MOSH-Insa-Toulouse/2024-2025-4GP-GregoryBibiloni-GuillaumeBarth/Android/face arrière.png

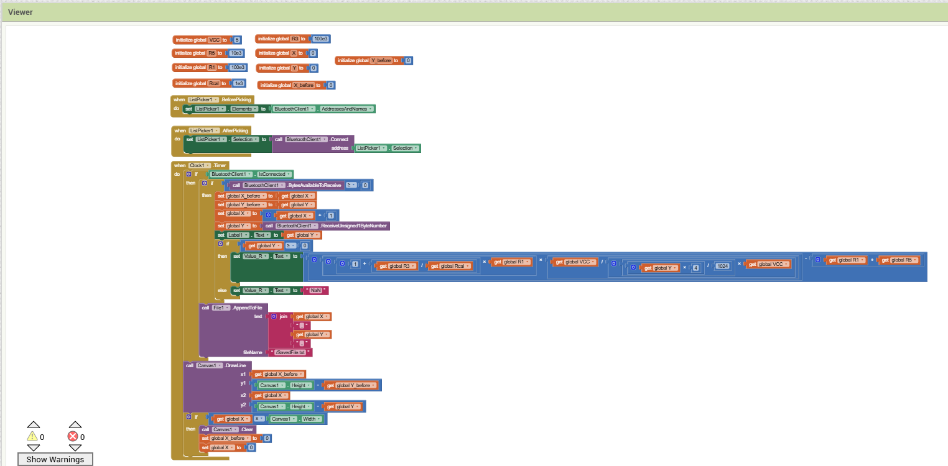
Android/face arrière.png
