MOSH-Insa-Toulouse/2024-2025-4GP-GregoryBibiloni-GuillaumeBarth/Android/face avant.png

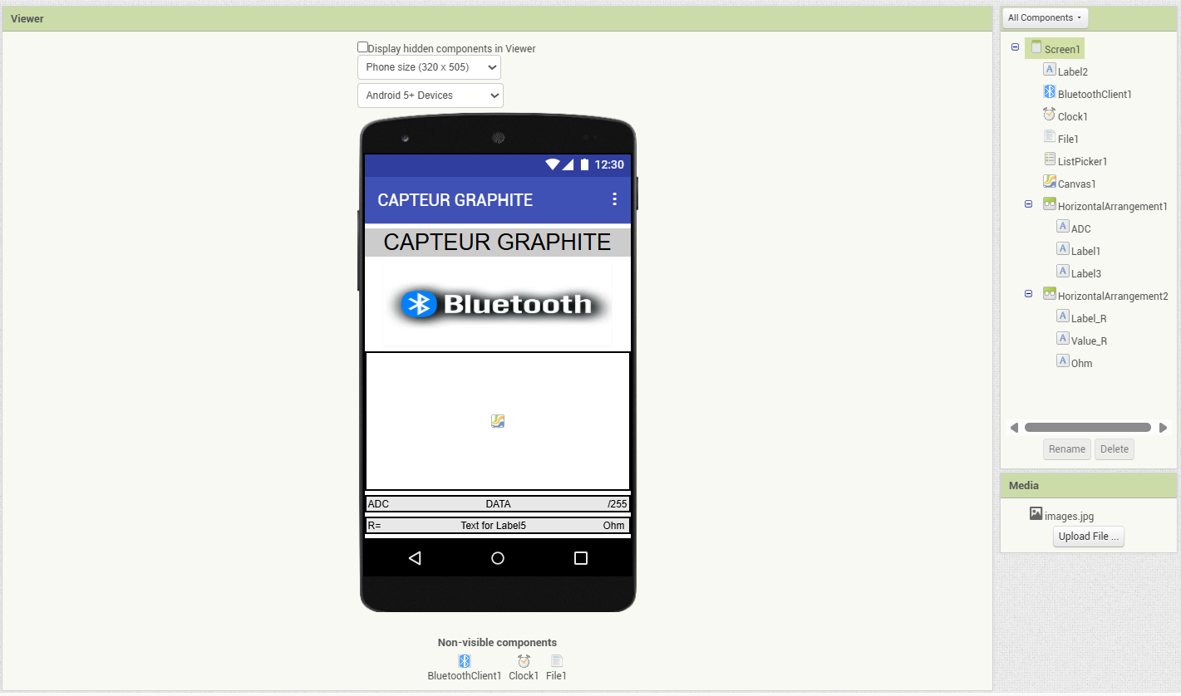
Android/face avant.png
