MOSH-Insa-Toulouse/2024-2025-4GP-GregoryBibiloni-GuillaumeBarth/KiCad/3D Models/4par1 female header/PBS1.27.png

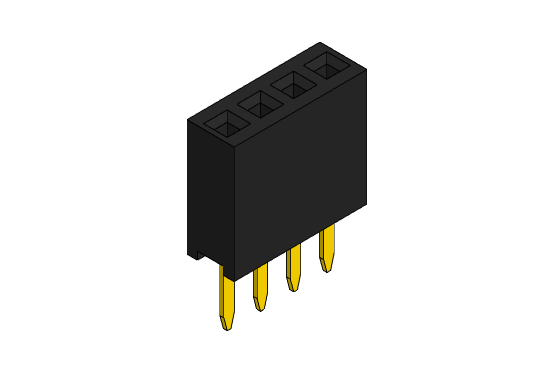
KiCad/3D Models/4par1 female header/PBS1.27.png
