MOSH-Insa-Toulouse/2024-2025-4GP-GregoryBibiloni-GuillaumeBarth/KiCad/3D Models/STEP/1x5.STEP

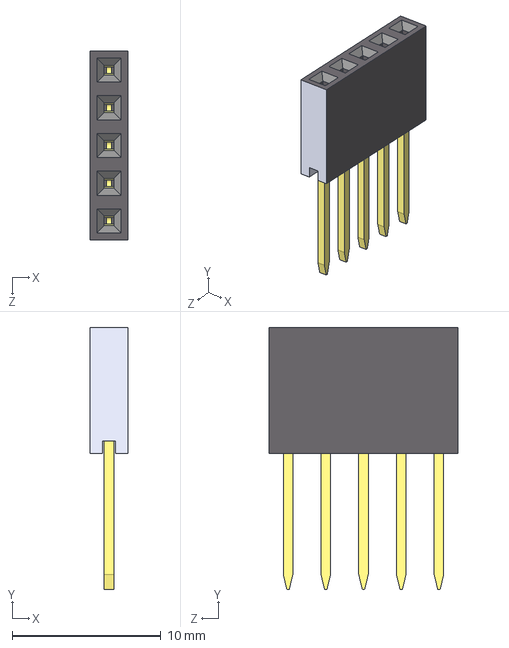
[picture p36: CAD file, 2025-03-13]
KiCad/3D Models/STEP/1x5.STEP
2.54 x 17.6 x 12.7 mm
