MOSH-Insa-Toulouse/2024-2025-4GP-GregoryBibiloni-GuillaumeBarth/KiCad/3D Models/Flex sensor/SolidEdge/FS-L-0095-103-ST - Top.stp

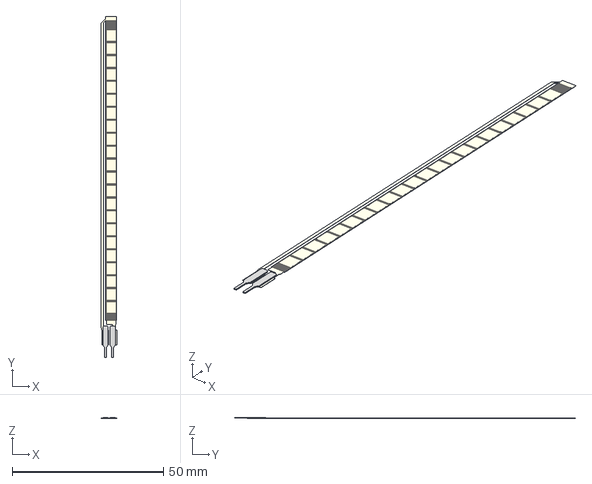
[picture p38: CAD file, 2025-03-13]
KiCad/3D Models/Flex sensor/SolidEdge/FS-L-0095-103-ST - Top.stp
5.17 x 112.8 x 0.292 mm
