MOSH-Insa-Toulouse/2024-2025-4GP-GregoryBibiloni-GuillaumeBarth/KiCad/3D Models/Rotary encodeur/Rotary Encoder -  ODG/sw2017 model/2.54 5PIN 90.SLDPRT

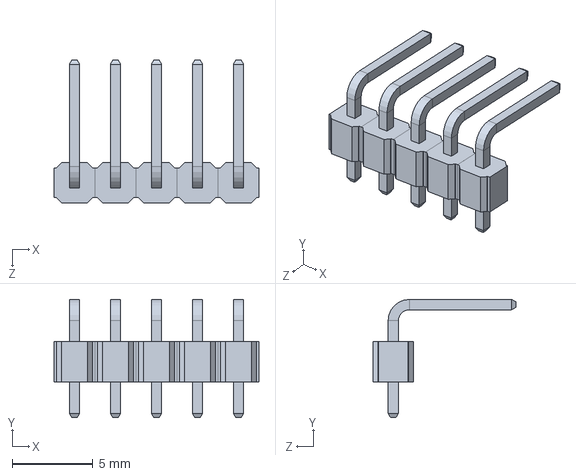
[picture p39: CAD file, 2025-03-13]
KiCad/3D Models/Rotary encodeur/Rotary Encoder - ODG/sw2017 model/2.54 5PIN 90.SLDPRT
12.7 x 7.32 x 8.85 mm
