MOSH-Insa-Toulouse/2024-2025-4GP-GregoryBibiloni-GuillaumeBarth/KiCad/3D Models/Rotary encodeur/Rotary Encoder -  ODG/sw2017 model/D-handle.SLDPRT

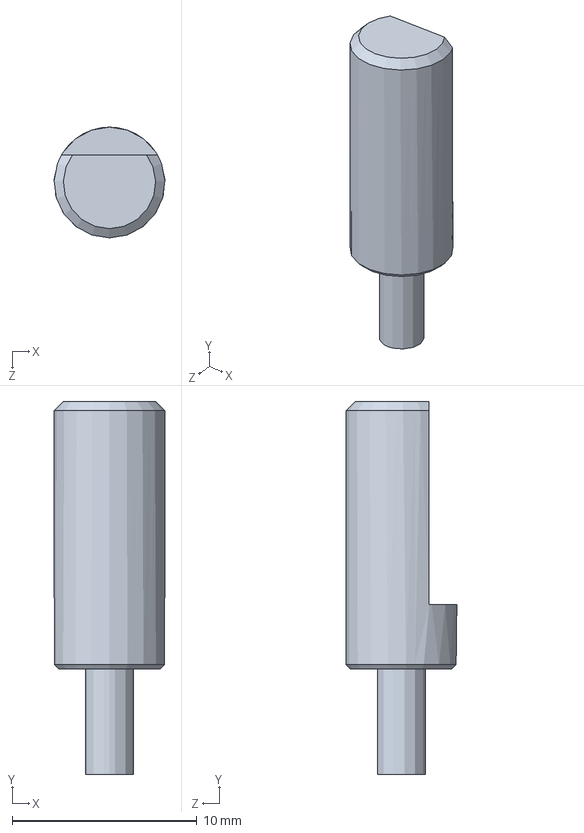
[picture p42: CAD file, 2025-03-13]
KiCad/3D Models/Rotary encodeur/Rotary Encoder - ODG/sw2017 model/D-handle.SLDPRT
6.00 x 20.2 x 6.00 mm
