MOSH-Insa-Toulouse/2024-2025-4GP-GregoryBibiloni-GuillaumeBarth/KiCad/3D Models/Rotary encodeur/Rotary Encoder -  ODG/sw2017 model/Rotary Encoder.SLDPRT

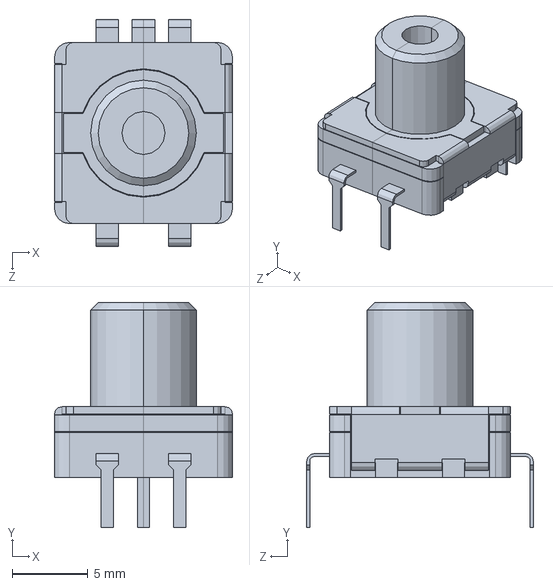
[picture p45: CAD file, 2025-03-13]
KiCad/3D Models/Rotary encodeur/Rotary Encoder - ODG/sw2017 model/Rotary Encoder.SLDPRT
11.8 x 14.9 x 15.0 mm
