MOSH-Insa-Toulouse/2024-2025-4GP-GregoryBibiloni-GuillaumeBarth/KiCad/3D Models/STEP/1x4.STEP

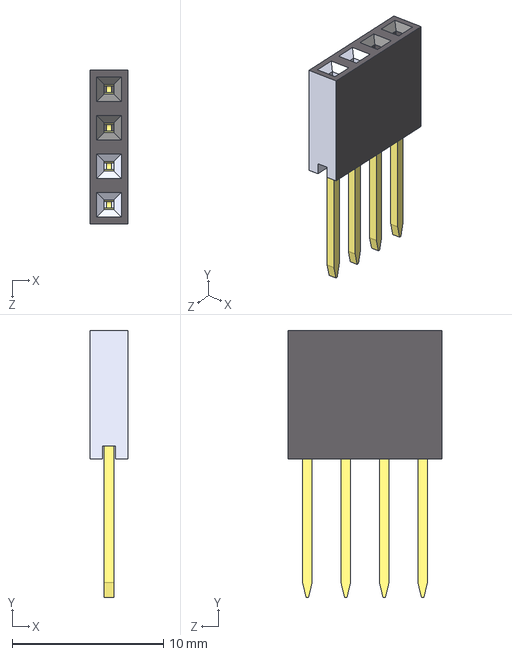
[picture p46: CAD file, 2025-03-13]
KiCad/3D Models/STEP/1x4.STEP
2.54 x 17.6 x 10.2 mm
