MOSH-Insa-Toulouse/2024-2025-4GP-GregoryBibiloni-GuillaumeBarth/KiCad/3D Models/4par1 female header/models3d/PBS1.27/PBS1.27-22R.step

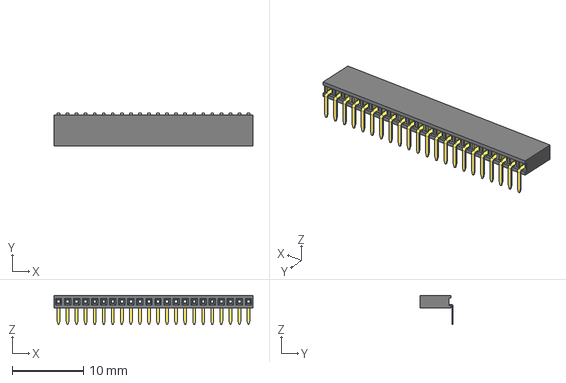
[picture p47: CAD file, 2025-03-13]
KiCad/3D Models/4par1 female header/models3d/PBS1.27/PBS1.27-22R.step
27.9 x 4.70 x 4.10 mm
