MOSH-Insa-Toulouse/2024-2025-4GP-GregoryBibiloni-GuillaumeBarth/KiCad/3D Models/STEP/pin header female 2.54mm_0.1in.STEP

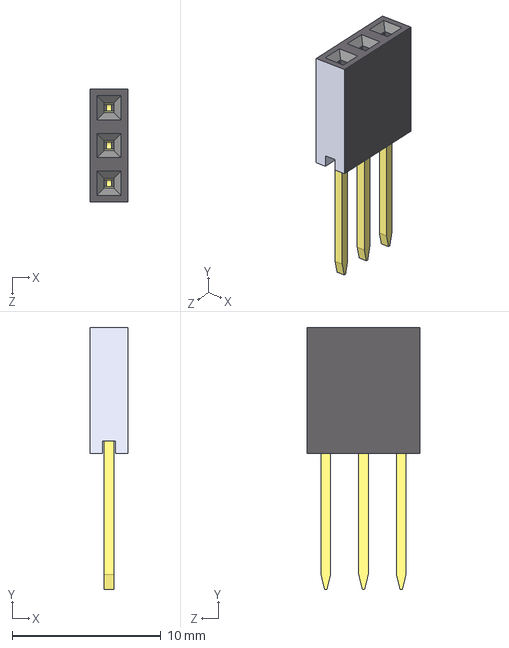
[picture p48: CAD file, 2025-03-13]
KiCad/3D Models/STEP/pin header female 2.54mm_0.1in.STEP
2.54 x 17.6 x 7.62 mm
