MOSH-Insa-Toulouse/2024-2025-4GP-GregoryBibiloni-GuillaumeBarth/KiCad/3D Models/STEP/1x10.STEP

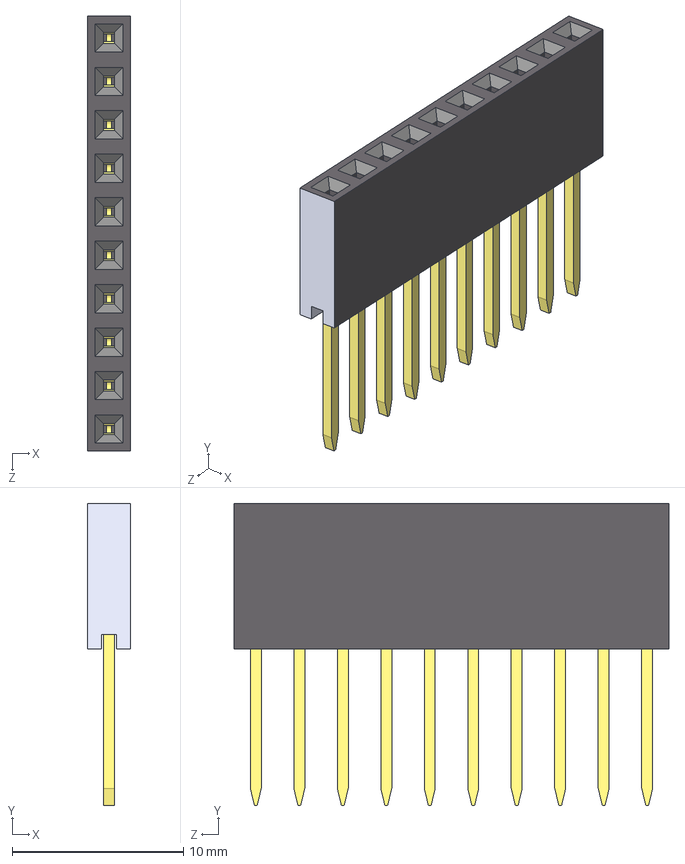
[picture p50: CAD file, 2025-03-13]
KiCad/3D Models/STEP/1x10.STEP
2.54 x 17.6 x 25.4 mm
